vives-project-xp/Aurora/Documenten/images/Diagram.png

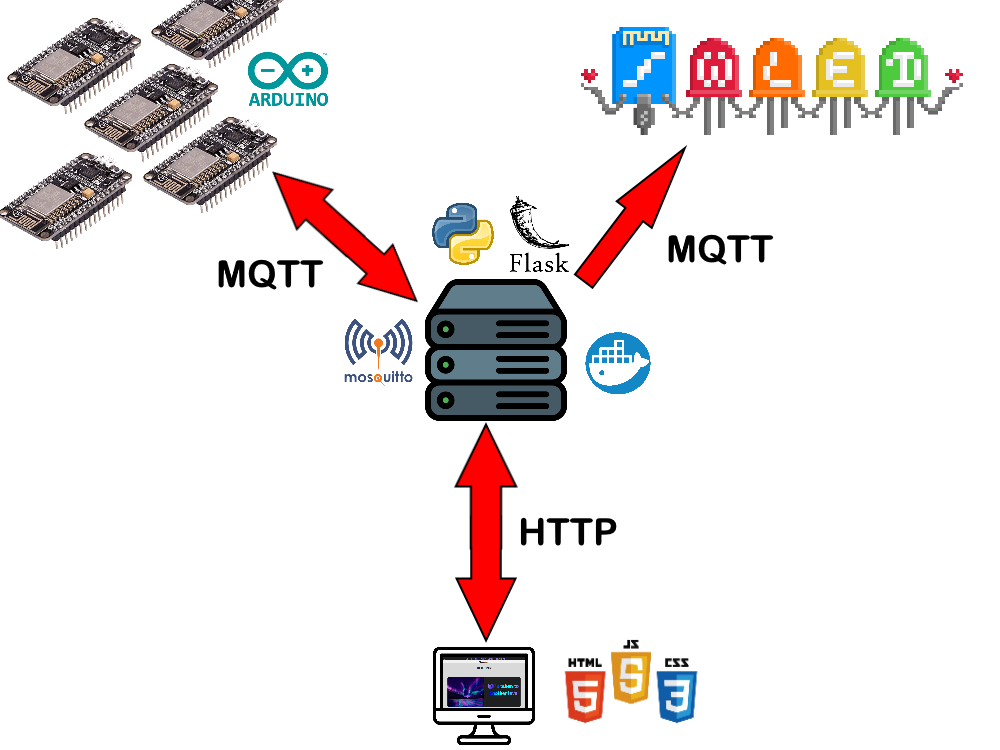
Documenten/images/Diagram.png
