vives-project-xp/Aurora/Documenten/images/Readme/Bridge lights.jpg

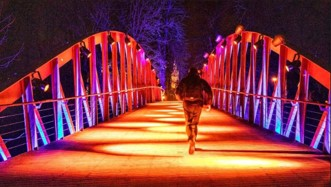
Documenten/images/Readme/Bridge lights.jpg
