vives-project-xp/Aurora/Documenten/IMG20230302144525.jpg

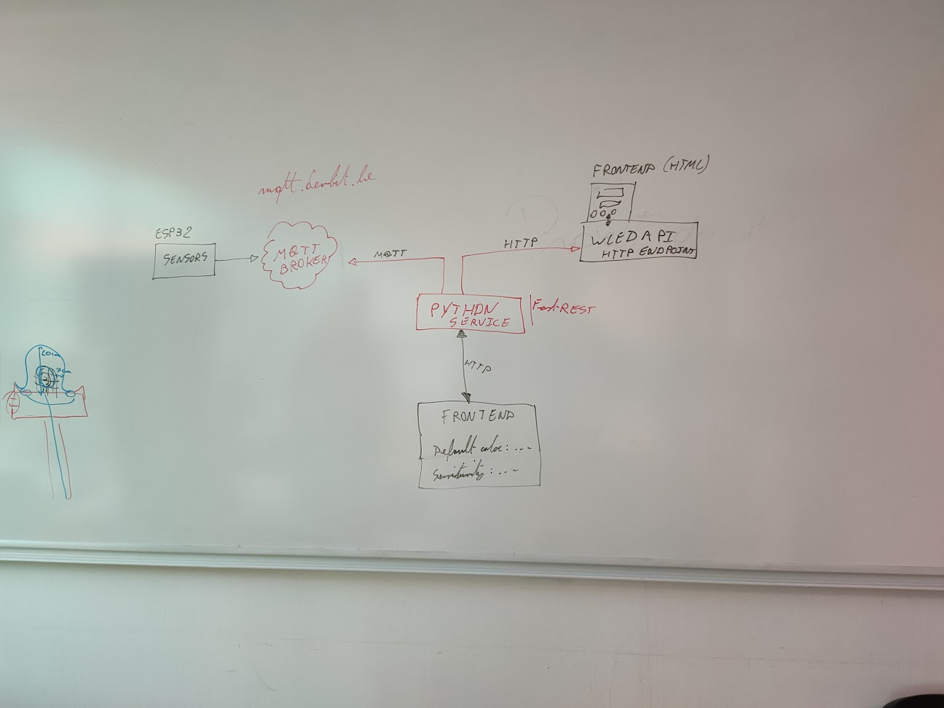
Documenten/IMG20230302144525.jpg
