vives-project-xp/Aurora/Documenten/IMG20230302163809.jpg

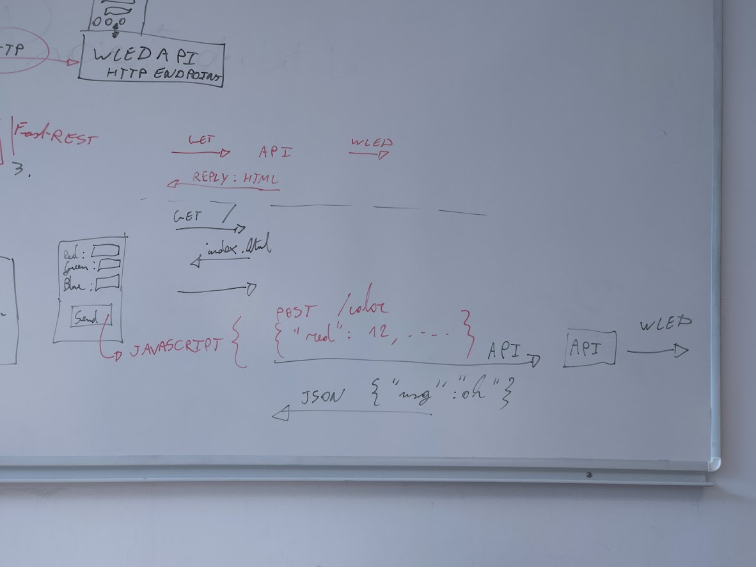
Documenten/IMG20230302163809.jpg
