vives-project-xp/Aurora/Documenten/Schema.jpg

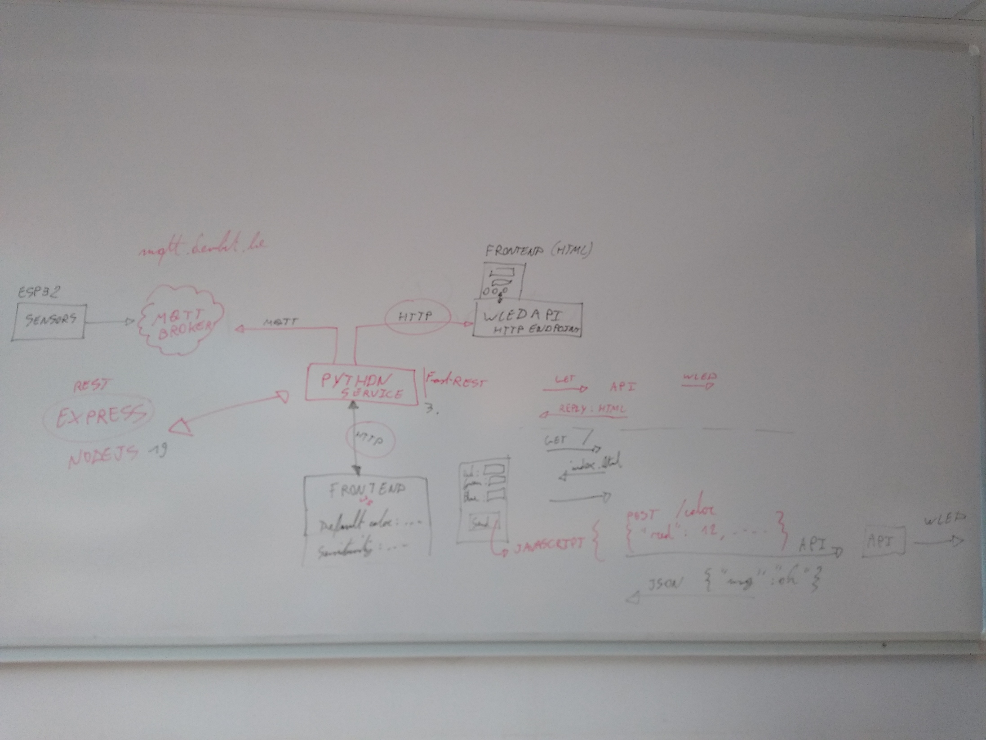
Documenten/Schema.jpg
