vives-project-xp/Aurora/Documenten/schema.png

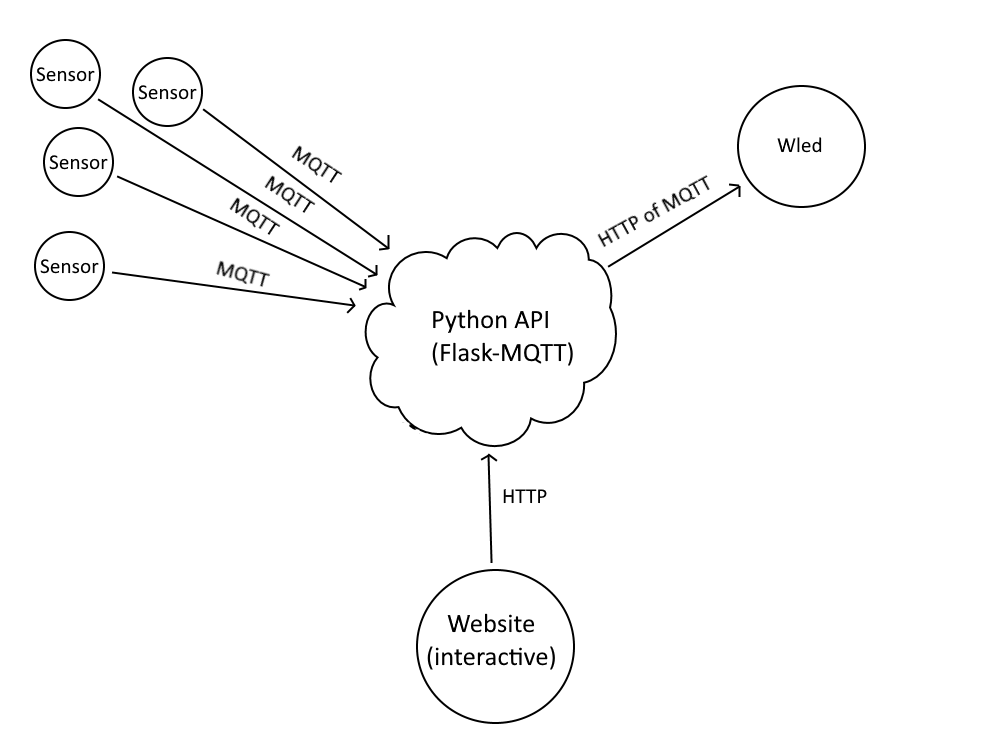
Documenten/schema.png
