vives-project-xp/Aurora/Video/images/Afbeelding1.jpg

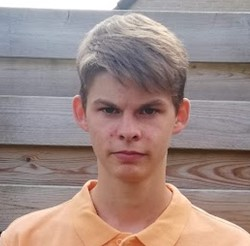
Video/images/Afbeelding1.jpg
