vives-project-xp/Aurora/Video/images/IMG_2686.jpg

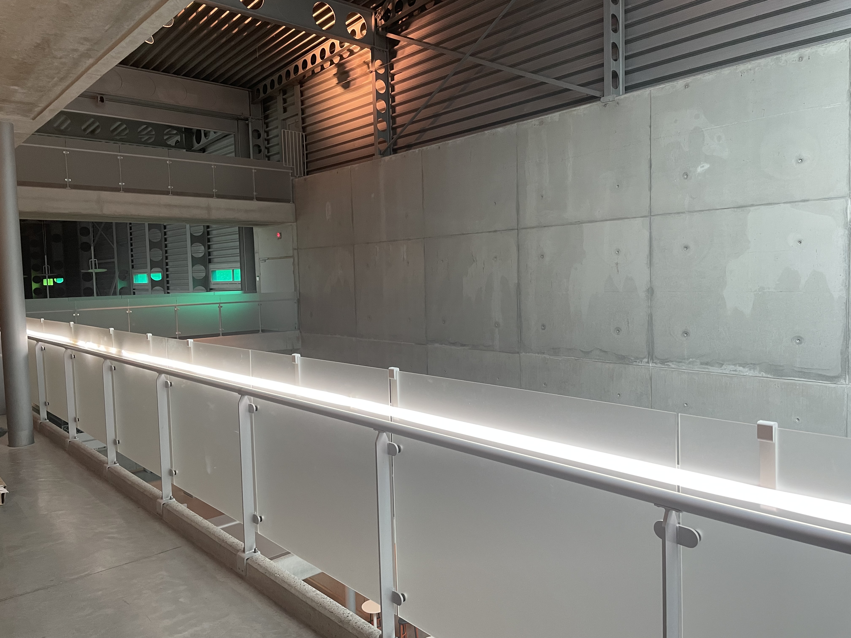
Video/images/IMG_2686.jpg
