vives-project-xp/Aurora/Video/images/IMG_2687.jpg

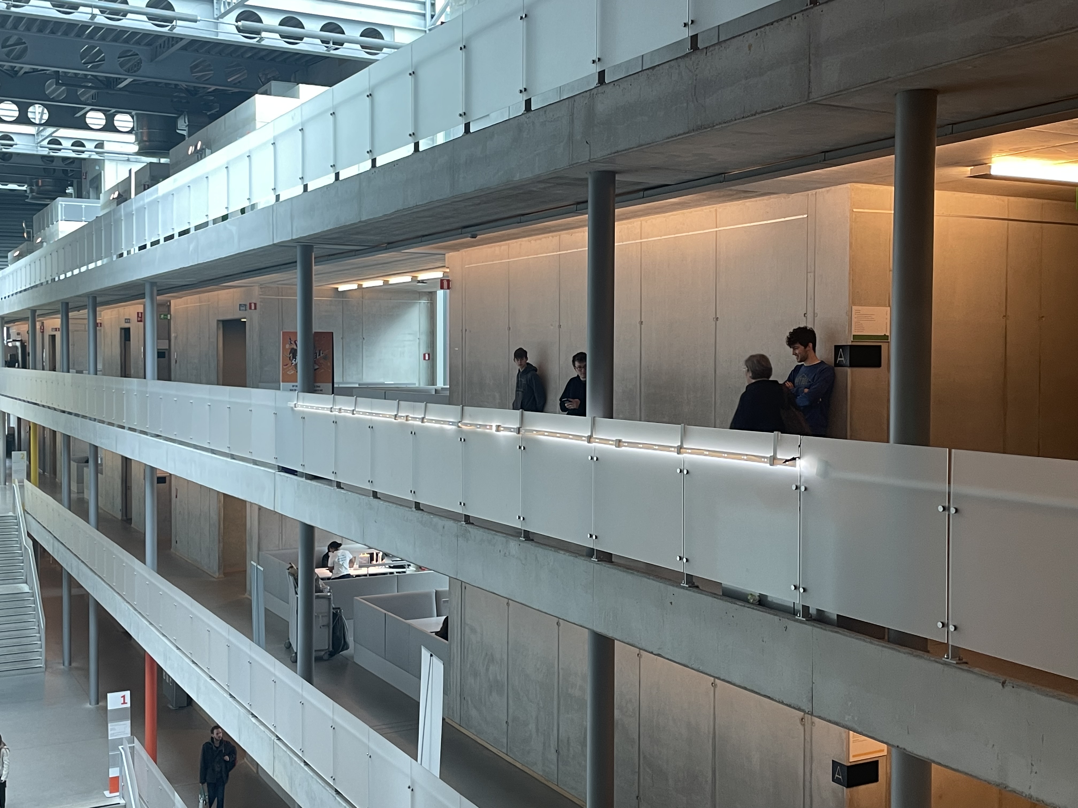
Video/images/IMG_2687.jpg
