vives-project-xp/Aurora/Video/images/Schermafbeelding 2023-05-04 153349.png

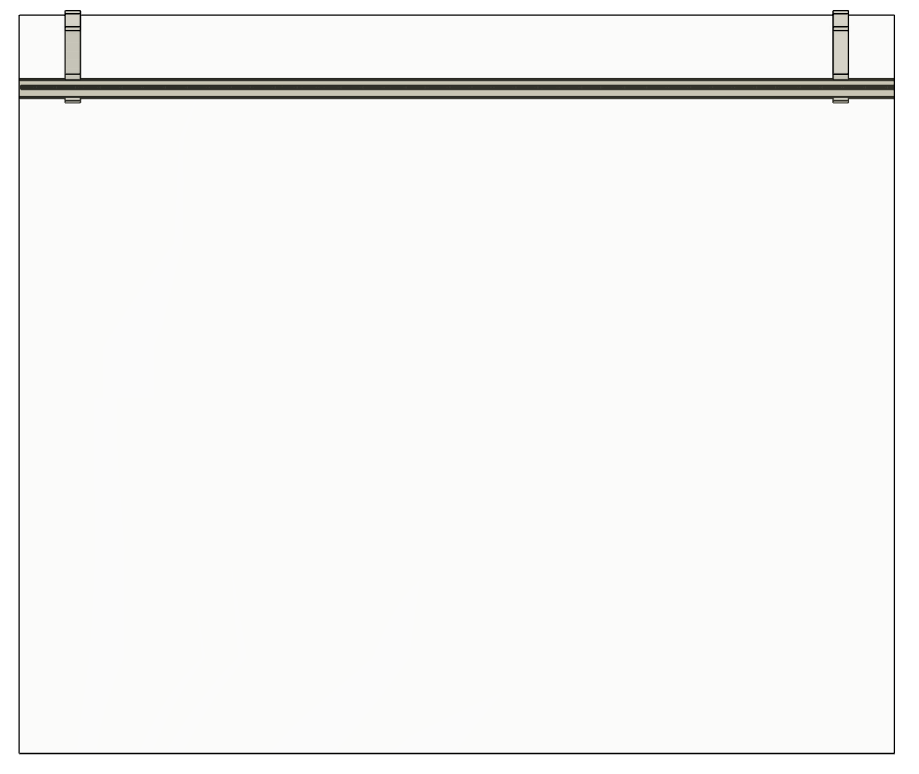
Video/images/Schermafbeelding 2023-05-04 153349.png
