vives-project-xp/Aurora/website/html/images/aitor.jpg

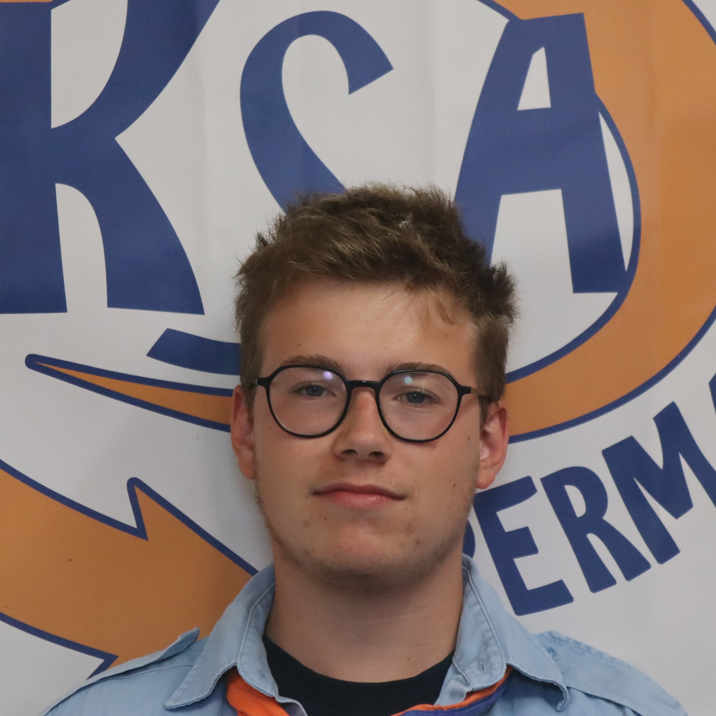
website/html/images/aitor.jpg
