vives-project-xp/Aurora/website/html/images/giphy.gif

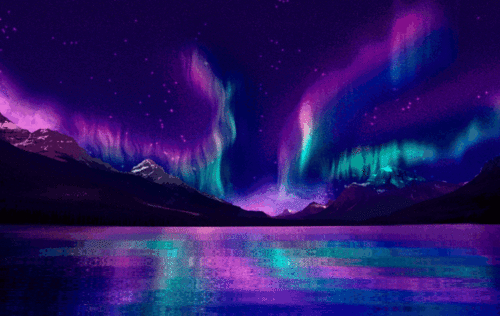
website/html/images/giphy.gif
