vives-project-xp/Aurora/website/html/images/led.jpg

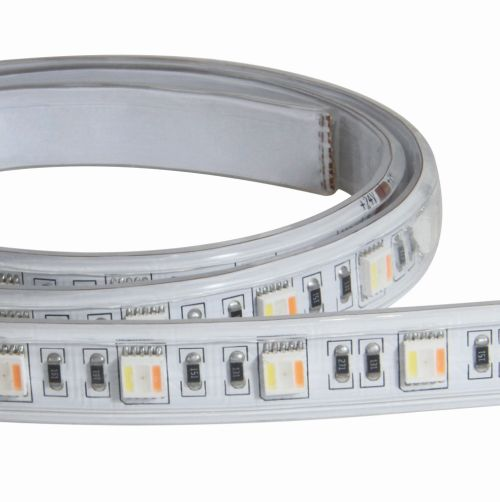
website/html/images/led.jpg
