vives-project-xp/Aurora/website/html/images/led.png

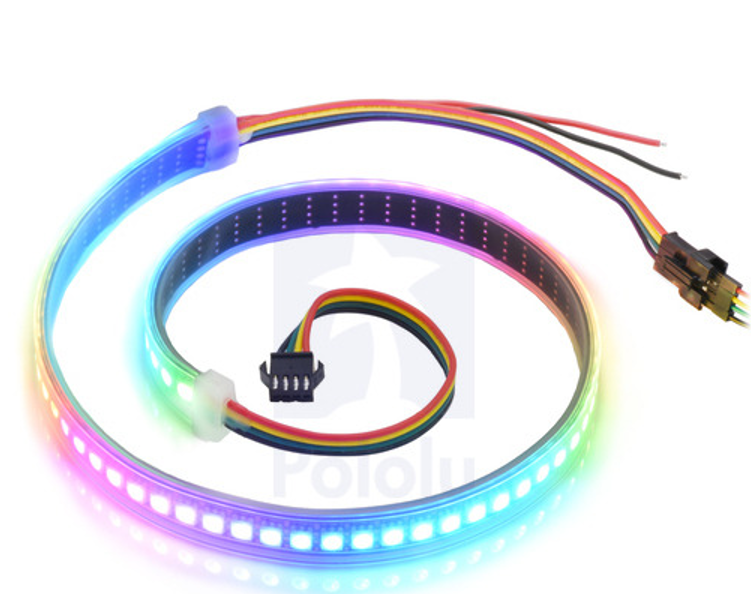
website/html/images/led.png
