vives-project-xp/Aurora/website/html/images/photo1.jpg

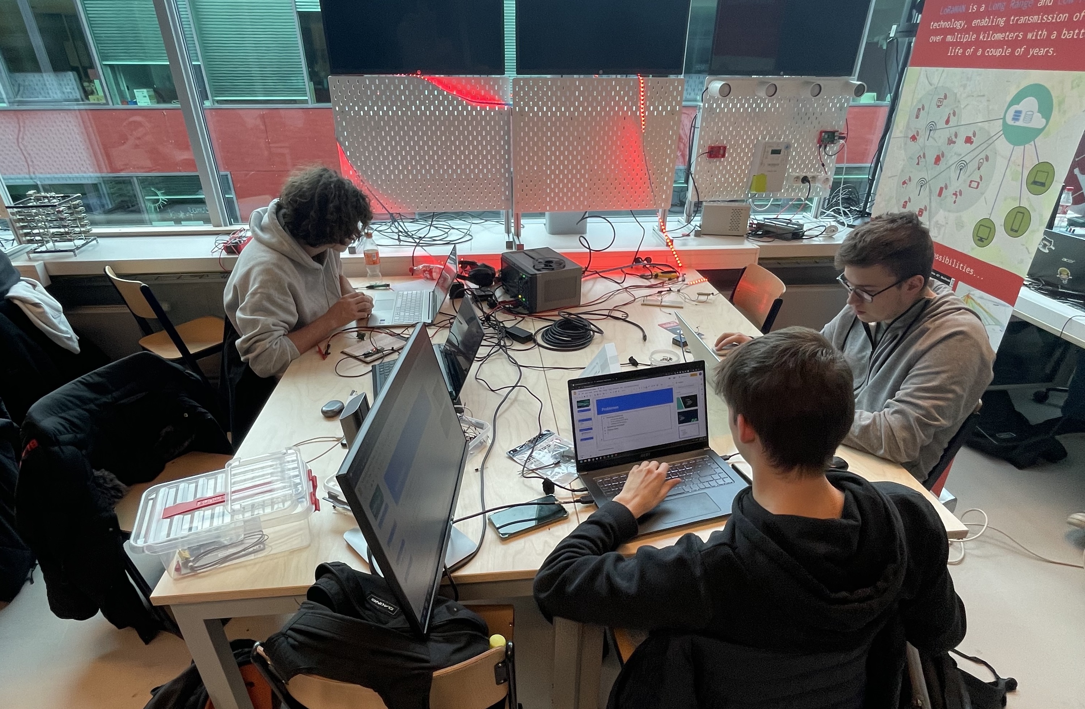
website/html/images/photo1.jpg
