vives-project-xp/Aurora/website/html/images/photo4.jpg

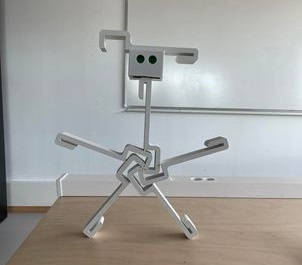
website/html/images/photo4.jpg
