vives-project-xp/Aurora/website/html/images/photo5.jpeg

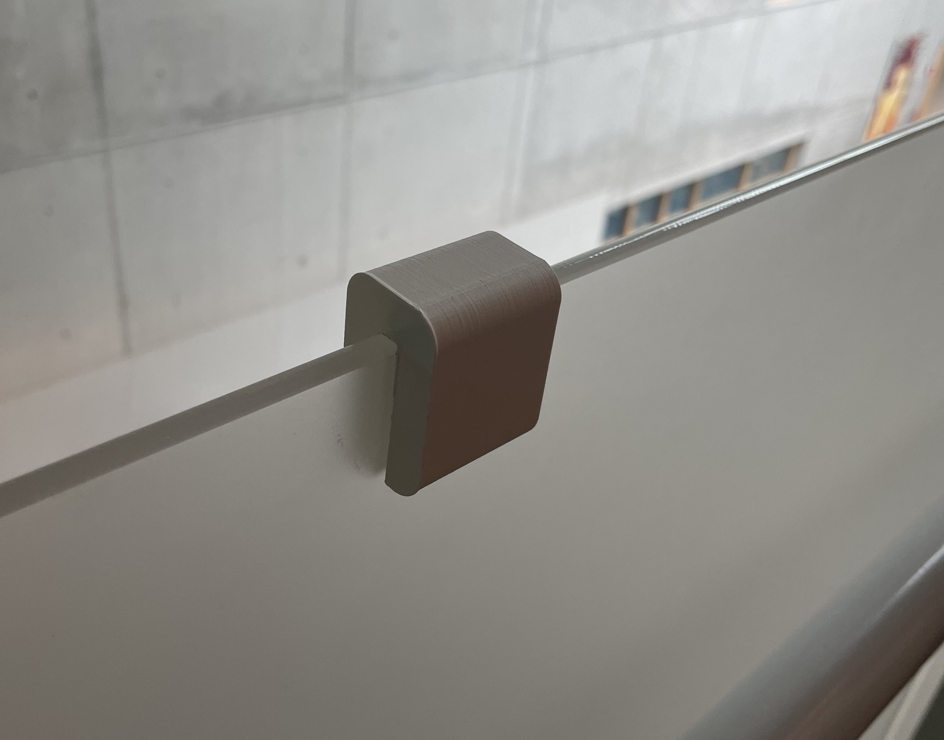
website/html/images/photo5.jpeg
