vives-project-xp/Aurora/website/html/images/photo7.jpeg

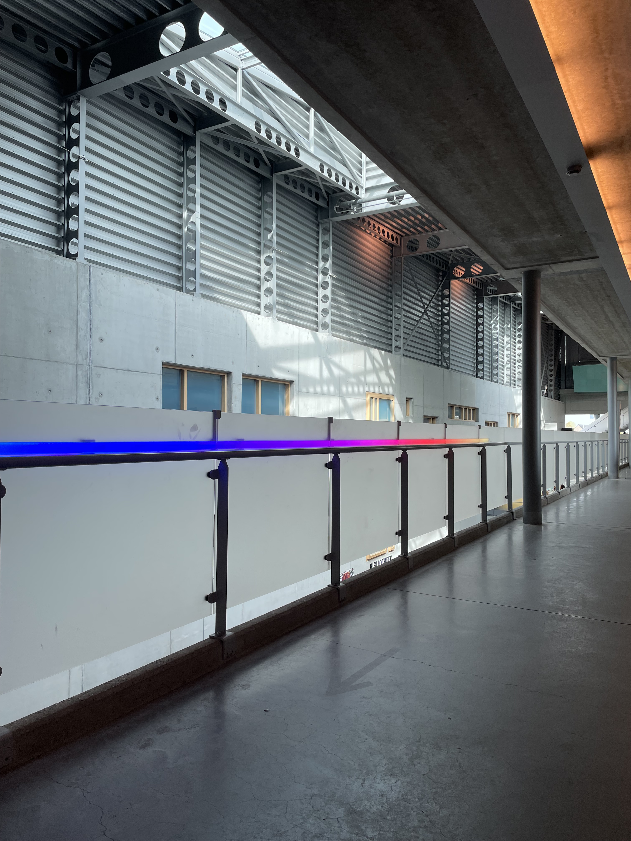
website/html/images/photo7.jpeg
