vives-project-xp/Aurora/website/html/images/planning.jpg

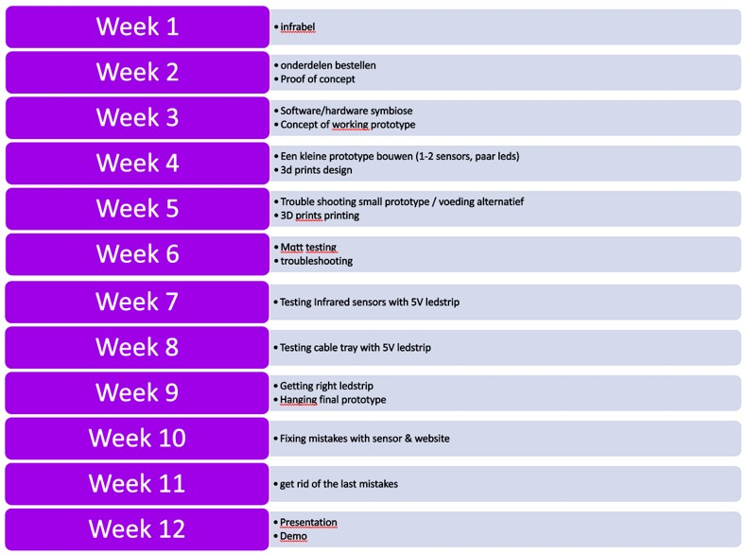
website/html/images/planning.jpg
