vives-project-xp/Aurora/website/html/images/ProfilePicThomas_v00.jpg

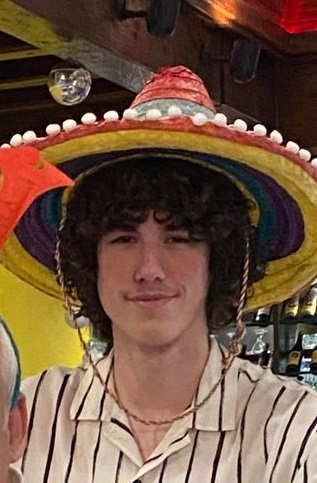
website/html/images/ProfilePicThomas_v00.jpg
