vives-project-xp/Aurora/website/html/images/ultrasonic.jpg

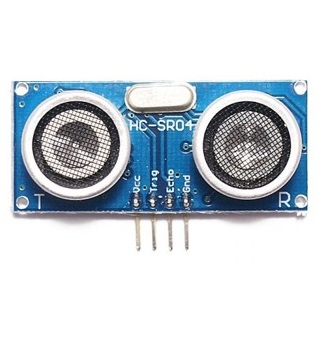
website/html/images/ultrasonic.jpg
