vives-project-xp/Aurora/website/html/images/voeding.jpg

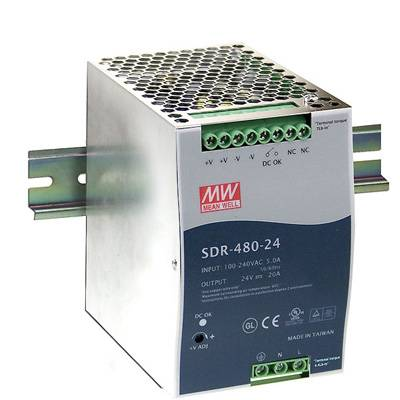
website/html/images/voeding.jpg
