vives-project-xp/Aurora/ESP_Sensors/config.h

namespace Sonic {

  namespace Config {

    const char * WIFI_SSID =              "YOUR_SSID";
    const char * WIFI_PASSWORD =          "YOUR_PASSWORD";
    const char * MQTT_BROKER_IP =         "BROKER_ADDRESS";
    const unsigned int MQTT_BROKER_PORT = 38884;
    const String MQTT_BASE_TOPIC =        "aurora/sensor";
  };
};  
