vives-project-xp/Aurora/PythonAPI/MQTT/MQTT ESP/MQTT_Test_Pub_SonicSensor/config.h

namespace Sonic {

  namespace Config {

    const char * WIFI_SSID =              "devbit";
    const char * WIFI_PASSWORD =          "Dr@@dloos!";
    const char * MQTT_BROKER_IP =         "broker.emqx.io";
    const unsigned int MQTT_BROKER_PORT = 1883;
    const String MQTT_BASE_TOPIC =        "aurora/sensor_1";

  };
};
